RyutaroMasuda/SoundProofingBox/RZ420_kh/computer_RZ420.SLDPRT

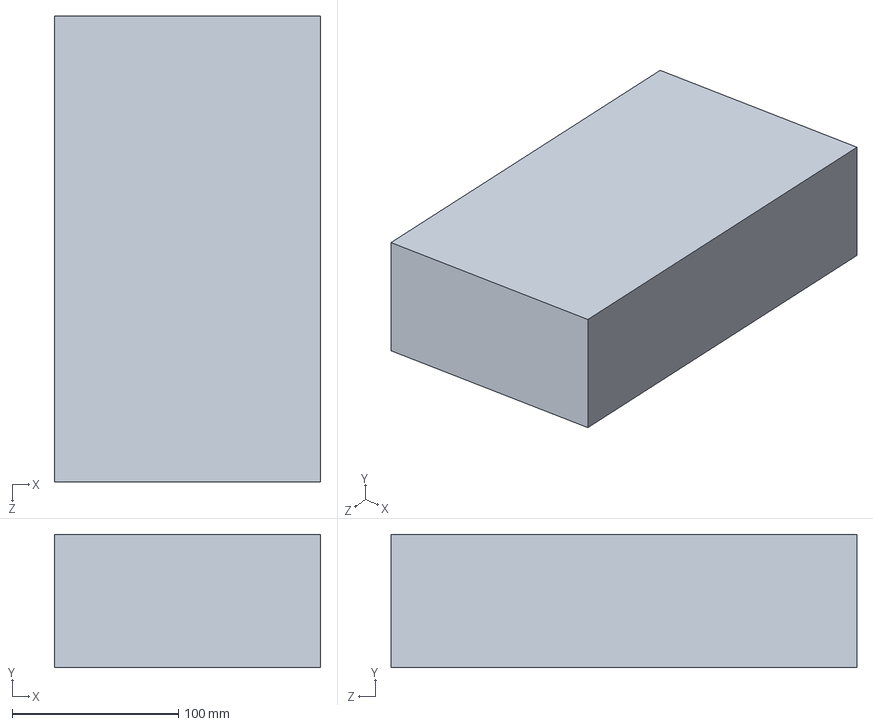
[picture p12: CAD file, 2025-01-08]
RZ420_kh/computer_RZ420.SLDPRT
160.0 x 80.0 x 280.0 mm
