RyutaroMasuda/SoundProofingBox/plate_left_large.SLDPRT

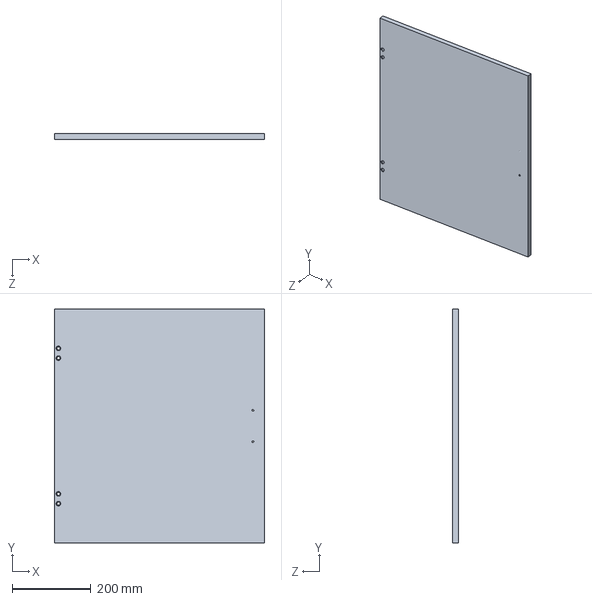
[picture p13: CAD file, 2025-01-08]
plate_left_large.SLDPRT
535.0 x 595.0 x 15.0 mm
