RyutaroMasuda/SoundProofingBox/Onimenut_m5.SLDPRT

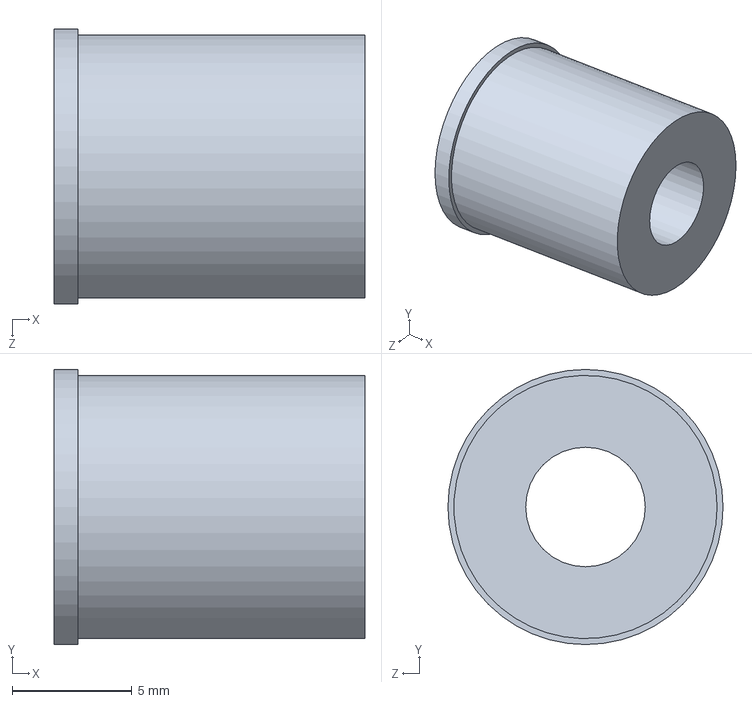
[picture p14: CAD file, 2025-01-08]
Onimenut_m5.SLDPRT
13.0 x 11.5 x 11.5 mm
