RyutaroMasuda/SoundProofingBox/plate_rightside.SLDPRT

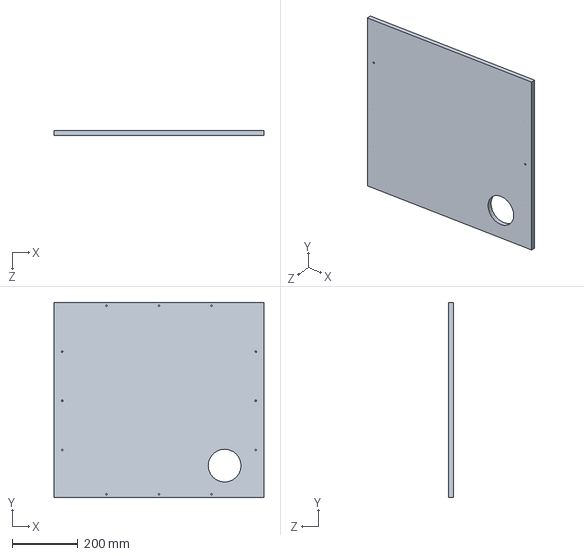
[picture p15: CAD file, 2025-01-08]
plate_rightside.SLDPRT
640.0 x 595.0 x 15.0 mm
