RyutaroMasuda/SoundProofingBox/plate_above.SLDPRT

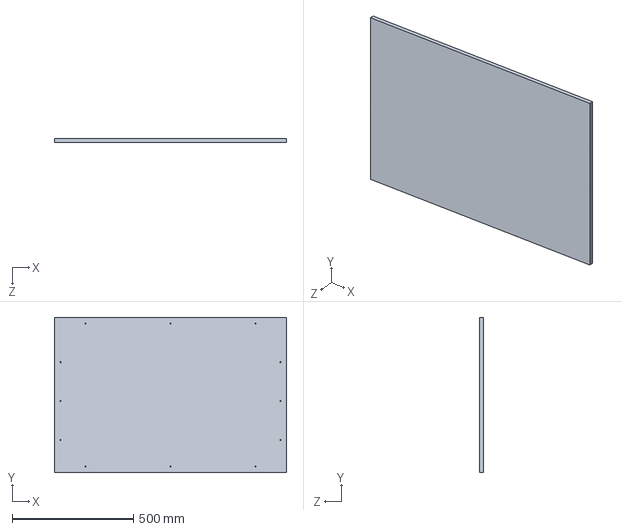
[picture p16: CAD file, 2025-01-08]
plate_above.SLDPRT
955.0 x 640.0 x 15.0 mm
