RyutaroMasuda/SoundProofingBox/s-assy-leftsmall.SLDASM

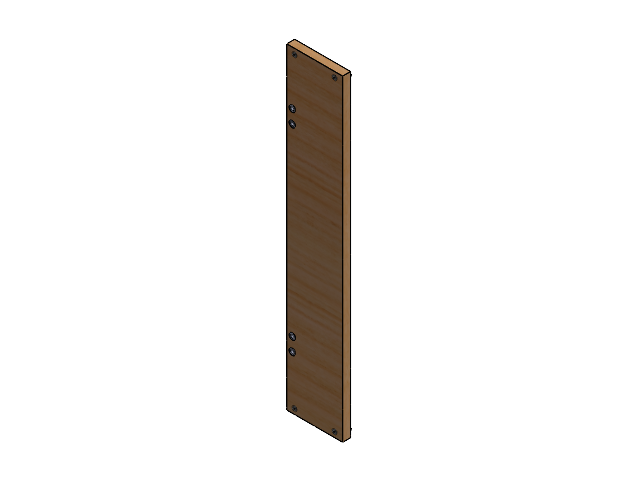
[picture p20: CAD file, 2025-01-08]
s-assy-leftsmall.SLDASM
plate_left_small
Onimenut_m5 x 4
MISUMI_E-GCBSTSR5-20 x 4
MISUMI_HNTP5-5 x 4
