RyutaroMasuda/SoundProofingBox/s-assy-rightside.SLDASM

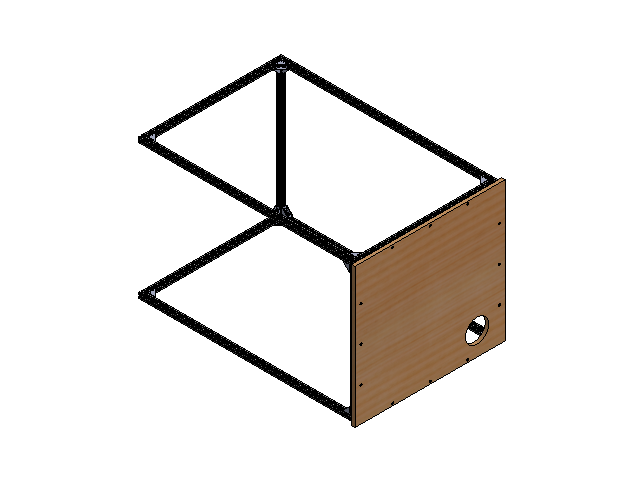
[picture p21: CAD file, 2025-01-08]
s-assy-rightside.SLDASM
plate_rightside
MISUMI_NFS5-2020-555.0 x 3
MISUMI_NFS5-2020-570.0 x 4
MISUMI_NFS5-2020-925.0 x 4
BRACKET_MISUMI_HBLFSN5 x 20
NEZI-M5x12L_MISUMI_HBLFSN5 x 40
MISUMI_HNTP5-5 x 52
MISUMI_E-GCBSTSR5-20 x 12
