RyutaroMasuda/SoundProofingBox/s-s-assy-bracket.SLDASM

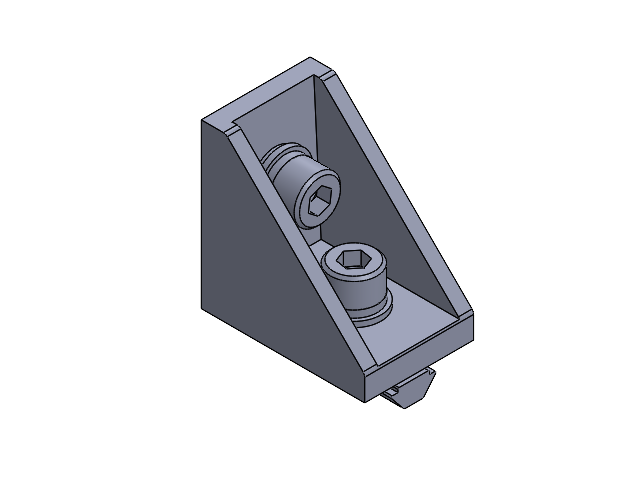
[picture p22: CAD file, 2025-01-08]
s-s-assy-bracket.SLDASM
BRACKET_MISUMI_HBLFSN5
NEZI-M5x12L_MISUMI_HBLFSN5 x 2
MISUMI_HNTP5-5 x 2
